lunavt6/Planda/reports and protocols/develop3 - CMF - report.pdf

# CMF report

Onderzoeksvragen
- Welke kleur voor het omhulsel spreekt kinderen van 2–6 jaar het meest aan?
- Welke kleur voor het omhulsel spreekt de ouders het meest aan?
- Welke textuur van het omhulsel is het meest comfortabel voor kinderen van 2–6 jaar?
- Welke kleur voor de oren spreekt kinderen van 2 – 6 jaar het meest aan?
- Welke kleur voor de oren spreekt de ouders het meest aan?

Protocol
Develop3 – CMF – protocol (https://drive.google.com/file/d/153IuJABdIxPPT9onyeNhh-75t1cRlU_d/view?usp=sharing)

Opstelling
Volgende prototypes werden gebruikt naast het tonen van de PowerPoints (zie bijlagen). Kleurgebruik van het omhulsel

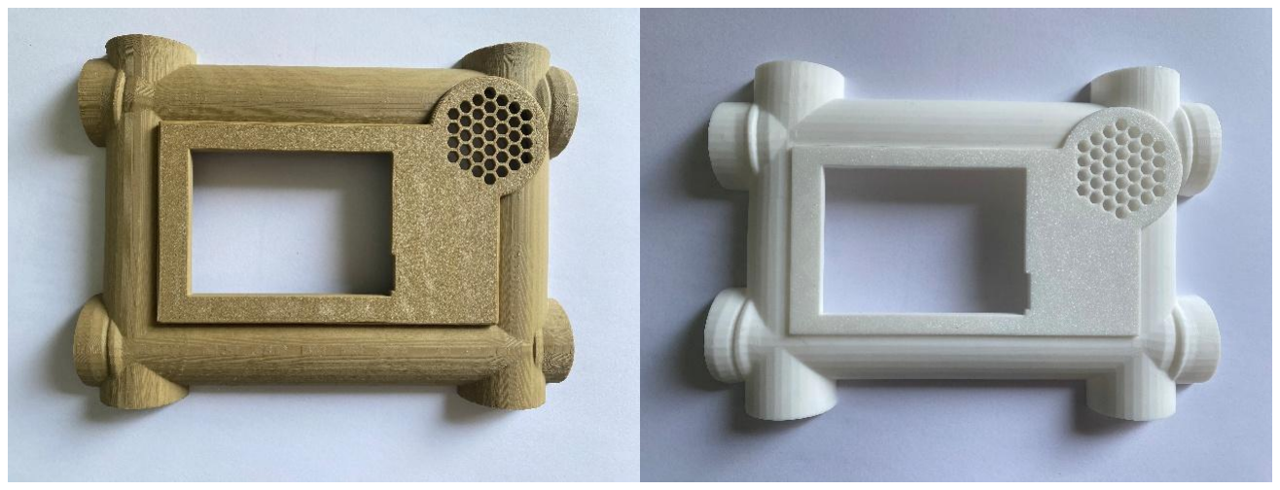
[picture p54: figure]

Figuur 1: Hout | Figuur 2: Wit

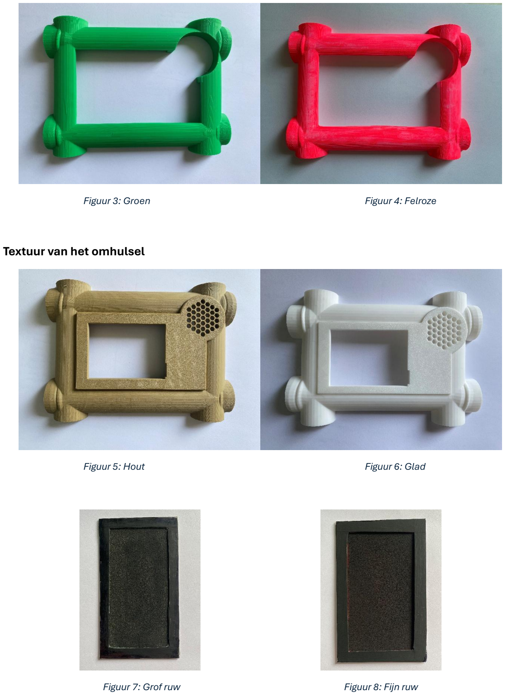
[picture p55: page 2]

Figuur 3: Groen | Figuur 4: Felroze

Textuur van het omhulsel

Figuur 5: Hout | Figuur 6: Glad
Figuur 7: Grof ruw | Figuur 8: Fijn ruw

Observatie
Kleur omhulsel
| Licht hout | Donker hout | Wit | Zwart | Groen | Oranje | Felroze
Kind 1 | | | | | | | X
Kind 2 | | | | | | | X
Kind 3 | | | | | | | X
Ouder 1 | X
Ouder 2 | X | | | | X

Textuur omhulsel
| Hout | Glad | Grof ruw | Fijn ruw
Kind 1 | | | | X
Kind 2 | | X
Kind 3 | | X
Ouder 1 | X
Ouder 2 | X | X

Kleur oren
| Doorzichtig | Transparant | Doorzichtig met rand | Roze | Blauw
Kind 1 | | | X
Kind 2 | | | X
Kind 3 | | | X
Ouder 1 | | | X
Ouder 2 | | | X

Analyse
Kleur omhulsel
Wat betreft het kleurgebruik voor het omhulsel gaven de kinderen duidelijk aan dat ze een voorkeur hebben voor felle, opvallende kleuren. Binnen de voorgestelde opties kwam vooral felroze als favoriete kleur naar voren. Dit staat in contrast met de mening van de ouders. Ouders verkiezen eerder kleuren die aansluiten bij het palet van hun interieur en daardoor minder storend aanwezig zijn in de leefomgeving. Hun voorkeur gaat voornamelijk uit naar neutrale, natuurlijke kleuren en zachte pastelkleuren.
Toch bleek uit de gesprekken dat ouders bereid zijn hierin compromissen te sluiten. Aangezien het product in de eerste plaat bedoeld is voor de kinderen, vinden zij het belangrijk dat het effectief gebruikt wordt en aantrekkelijk is voor hun kind. Wanneer felle kleuren ervoor zorgen dat de panda vaker gebruikt wordt of de interesse van het kind vergroot, staan ouders er dus voor open om af te wijken van hun eigen persoonlijke smaak.

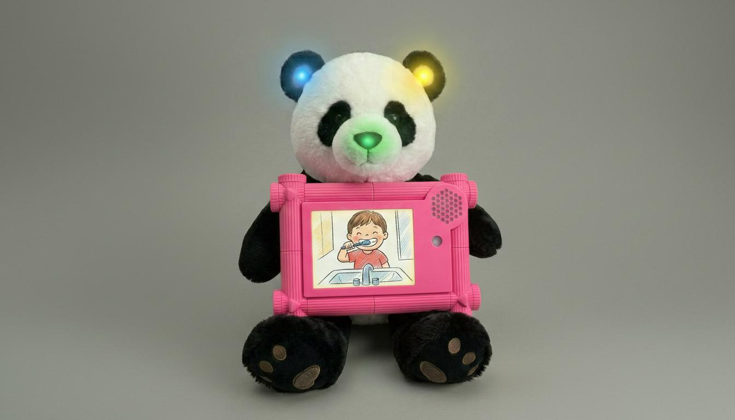
[picture p56: figure]

Figuur 9: Resultaat kleur omhulsel
Hoewel felroze het vaakst gekozen werd als kleur voor het omhulsel, dient opgemerkt te worden dat enkel meisjes deelnamen aan de bevraging. De resultaten kunnen daardoor beïnvloed zijn door persoonlijke of stereotype kleurvoorkeuren en zijn mogelijk niet representatief voor alle kinderen.

Textuur omhulsel
Bij de keuze van de textuur waren de meningen meer verspreid. De antwoorden liepen uiteen tussen de verschillende opties: hout, glad en fijn ruw. Vooral de ouders gaven aan dat ze de houttextuur aantrekkelijk vonden, omdat deze een warme, natuurlijke uitstraling heeft. Het materiaal oogde volgens hen rustgevend en stijlvol.
Toch werd hierbij ook rekening gehouden met het feit dat het uiteindelijke product geen houtkleur zal hebben. Hierdoor zou de houttextuur minder geloofwaardig of passend kunnen overkomen in het definitieve ontwerp. Daarom werd opnieuw gekeken naar de voorkeuren van de kinderen, aangezien zij toch wel de belangrijkste gebruikers van het product zijn.
Uit hun antwoorden bleek dat een gladdere textuur het meest aanspreekt. Een glad oppervlak werd door hen als aangenamer en zachter ervaren, wat beter aansluit bij het speelse en knuffelbare karakter van de panda. Bovendien zorgt een gladde afwerking voor een eenvoudiger en rustiger beeld, waardoor het ontwerp niet te druk wordt.

Kleur oren
Bij de keuze van de oren was er meteen een duidelijke favoriet. Zowel de kinderen als de ouders kozen unaniem voor de optie met een zwart randje. Deze versie werd als de mooiste en meest afgewerkte ervaren. Vooral het zwarte randje rond de oren maakte volgens hen een groot verschil. Daardoor zijn de oren beter zichtbaar en krijgt de panda meer karakter.
Ook zorgde deze optie ervoor dat de panda een herkenbare uitstraling kreeg, want de oren sluiten zo beter aan bij de rest van het ontwerp. Hierdoor oogt het geheel rustiger en samenhangender. Hierdoor kwam de panda aantrekkelijker over dan bij de andere opties.

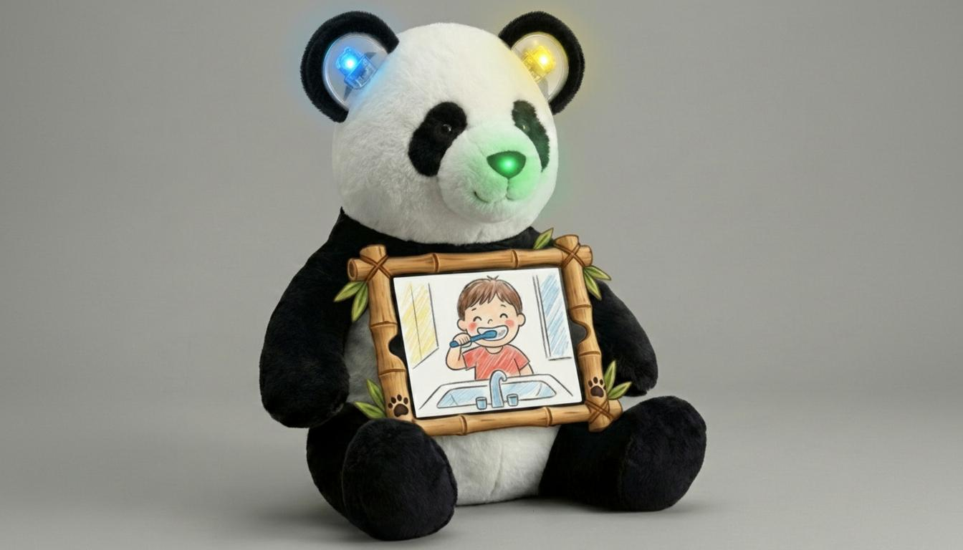
[picture p57: figure]

Figuur 10: Resultaat kleur oren

Conclusie
Uit de analyse blijkt dat kinderen vooral een voorkeur hebben voor felle kleuren en een speels ontwerp, terwijl ouders eerder kiezen voor rustige en natuurlijke tinten. Toch zijn ouders bereid om dit aan te passen als het product daardoor aantrekkelijker wordt voor het kind. De kinderen blijven dus de belangrijkste doelgroep. Daarnaast komt uit de analyse van de textuur naar voren dat een gladde afwerking het meest geschikt is, omdat deze door kinderen als zacht en prettig wordt ervaren en het speelse karakter van de panda versterkt. Ook bij de oren is er een duidelijke overeenstemming: zowel kinderen als ouders verkiezen de variant met een zwart randje, omdat dit zorgt voor meer herkenbaarheid, karakter en een mooi afgewerkt geheel.
De beste keuzes voor het ontwerp zijn daarom een felroze omhulsel, een gladde textuur en oren met een zwart randje. Dit zorgt voor een speels, herkenbaar en aantrekkelijk geheel dat tegelijk voldoende samenhang en rust behoudt.

Tijdens deze fase zijn de volgende design requirements ontstaan.
- Het omhulsel is felroze of een andere felle kleur gericht op de voorkeur van het kind.
- Het oppervlak is glad.
- De oren hebben een zwart randje.

Bijlagen
Develop3 – CMF – kleur omhulsel (https://drive.google.com/file/d/1jtBIYcoHiLNUWgVYdP9SYzcHUyG76-D9/view?usp=sharing) Develop3 – CMF – kleur oren (https://drive.google.com/file/d/1XNqXtDPErmhQJFLdnw9bNmKRSQDc-u7y/view?usp=sharing)
