lunavt6/Planda/reports and protocols/develop1 - literatuuronderzoek - data.pdf

# Literatuuronderzoek data

1. https://www.oudersvannu.nl/kind/de-ontwikkelingsfases-van-je-kind~a67eb44d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 (https://www.oudersvannu.nl/kind/de-ontwikkelingsfases-van-je-kind~a67eb44d)
- 2 – 3 jaar (peuter)
- peuterpuberteit, driftbuien
- overdag zindelijk worden
- begint zich te interesseren in poepen en plassen en kan ook aangeven wanneer hij moet
- middagslaapje wordt overgeslaan
- leert traplopen, rennen en springen
- kan in de speeltuin op steeds meer toestellen, buitenspelen
- fijne motoriek
- leert tekenen (begin: krassen) -> spieren van vingers en handen sterker,
- oefenen van zelf aan- en uitkleden
- samen spelen nog moeilijk
- peuter begrijpt al bijna alles wat je zegt en kan zelf korte zinnetjes terugzeggen
- 3 – 4 jaar (peuter)
- waarom? (nieuwsgierigheid)
- krijgt grote fantasie en gaat magisch denken
- goed rollenspellen doen
- kunnen ook angsten ontstaan (monster in de slaapkamer)
- driftbuien nog altijd, maar kunnen toch al wat beter zich beheersen dan vorige fase
- beginnen begrijpen van gevoelens van zichzelf en anderen
- besef krijgen van wat goed en fout is
- schuldig voelen
- geen middagdutje
- naar kleuterschool gaan -> belangrijk dat bepaalde zaken zelfstandig kunnen
- oefenen van jas en schoenen aandoen, billen afvegen
- 4 – 6 jaar (kleuter)
- Gaat naar school
- Nieuwe wijsheden en vaardigheden
- Vrienden maken
- Naar school gaan vraagt veel energie
- Vermoeidheid
- Driftbuien
- Terugval in zindelijkheid -> tijdelijk
- Terugval in duimen -> tijdelijk
- Meer interesse in eigen lichaam en dat van anderen
- Doktertje spelen
- Vader-en-moedertje spelen
- Verliefd zijn
- Melktanden beginnen uit te vallen
- Motorisch

- Hoger klimmen
- Harder fietsen
- Van grote hoogte naar beneden springen
2. https://www.kindengezin.be/nl/thema/ontwikkeling-en-gedrag
- Grove motoriek
- Hoofd optillen: rond 3 maanden
- Rollen: 4 à 5 maanden
- Zitten
- Met steun: rond 6 maanden
- Alleen: rond 9 maanden
- Kruipen: vanaf 6 à 9 maanden
- Staan: vanaf 6 à 9 maanden
- Lopen: rond 14 à 15 maanden eerste stapjes
- Fijne motoriek
- Grijpreflex
- Pasgeboren baby: handjes altijd gebald tot vuistjes
- 2 maanden: handjes af en toe open en dicht
- 3 maanden: handjes meestal open
- Grijpen:
- Vanaf 3, 5 à 6 maand: gericht grijpen en later ook vast te houden
- Tussen 6 en 9 maanden: voorwerp van de ene naar de andere hand overgeven en 2 voorwerpen tegelijk vasthouden
- Tussen 9 en 12 maanden: klein voorwerp oppakken tussen duim en wijsvinger en/of middenvinger = pincetgreep / tweevingergreep
- Onderzoeken met de handen: tussen 6 en 9 maanden
- met de vlakke hand tegen dingen slaan
- voorwerpen tegen elkaar slaan
- voorwerpen opzettelijk laten vallen
- een handje in een beker stoppen
- vanaf 12 maanden: complexere bewegingen
- Eten met een vork: rond 18 maanden -> wel nog lastig
- Tekenen
- Rond 12 maanden: krassen
- Rond 2 jaar: bewegingen meer beheerst, krassen worden krabbels
- Rond 3 jaar: vormen zichtbaar: losse lijn, kruis, zigzaglijn, vierkant, …
- Na 3 jaar:
- Herkennen wat het getekend heeft, vb rondje -> gezicht of de zon getekend
- Uitbeeldend tekenen
- Meestal mensen en gezichten getekend
- Later armen en benen rechtstreeks aan hoofd getekend = kopvoeters
- Nog later: lijf erbij getekend
- Volgende fase
- Op voorhand plannen wat er op het papier moet komen

- Tekenen van tafereel
- Rond 8 à 9 jaar: tekenen van beelden uit de realiteit, wat ze zien
- Taalontwikkeling
- 15 maanden tot 3 jaar: peuter
- Kent en begrijpt al heel wat woorden
- Vanaf 18 maanden:
- zinnen maken van 2 woorden
- leren van nieuwe woorden
- stelt vragen aan iedereen rondom hem/haar
- tussen 2 en 3 jaar
- zinnen van 3 tot 5 woorden
- meer en meer verschillende woorden gebruiken
- 3 tot 6 jaar: kleuter
- 3 jaar: werkwoorden en meervouden leren gebruiken
- Begrijpen meer en meer wat kleuter zegt
3. https://www.nji.nl/kennis/ontwikkeling/peuter-de-algemene-ontwikkeling
4. https://www.nji.nl/kennis/ontwikkeling/kleuter-de-algemene-ontwikkeling -> zelfde dingen als eerste
5. https://doomijn.nl/blog/de-ontwikkelingsfasen-van-een-kind/
- Motorische ontwikkeling van een peuter
- Meer zelfstandig doen
- Ontwikkelen grove motorische vaardigheden: lopen, rennen, springen, hinkelen, traplopen en fietsen met zijwieltjes
- Ontdekken van activiteiten zoals bouwen, kleuren, kleien, voetballen en verven
- Experimenteren met materialen -> stimuleren van grove en fijne motoriek
- Ontwikkelen fijne motoriek: potlood vasthouden met pengreep ipv vuistgreep
- Cognitieve ontwikkeling van een peuter
- Groei in taalbegrip: peuter begrijpt steeds beter wat er tegen hem gezegd wordt
- Eenvoudige opdrachten uitvoeren
- Vragen beantwoorden
- Ontstaan kleine gesprekjes -> weten wat er in het kind omgaat
- Spraak- en taalontwikkeling van een peuter
- Actief praten en brabbelen
- Eerste echte woorden ontstaan
- Leren ongeveer 3 nieuwe woorden per dag
- Van losse woorden naar twee-woordzinnen
- Ontstaan van korte verhaaltjes en steeds langere, complexere zinnen
- Sociaal-emotionele ontwikkeling van een peuter
- Eigen wil en ik-besef
- Nee-fase, peuterpuberteit en driftbuien
- Nieuwsgierig
- Ontdekken dat wereld groter is dan hun vertrouwde omgeving -> angst en onzekerheid

- Motorische ontwikkeling van een kleuter
- Meer lichaamsbeheersing en soepelere bewegingen
- Starten van zwemles en fietsen zonder zijwieltjes
- Veters strikken en tekeningen worden gedetailleerder
- Melktanden vallen uit
- Naar school gaan
- Cognitieve ontwikkeling van een kleuter
- Leren
- Spelend leren
- Later: leren
- Hoeveelheden
- Plaats
- Tijd
- Ruimtelijke verhouding
- Oorzaak – gevolg
- Spraak- taalontwikkeling van een kleuter
- Letters herkennen
- Leren schrijven
- Complexere taal gebruiken
- Sociaal-emotionele ontwikkeling van een kleuter
- Ontwikkeling van geweten en schaamtegevoelens
- Magisch denken
- Zelfbeeld
- Assertiviteit, morele ontwikkeling, rechtvaardigheidsbesef, identificatie met ouders
6. https://www.ncj.nl/wp-content/uploads/media-import/docs/d5771c50-bac7-4fb6-a307-e302b14d664b.pdf (https://www.ncj.nl/wp-content/uploads/media-import/docs/d5771c50-bac7-4fb6-a307-e302b14d664b.pdf)

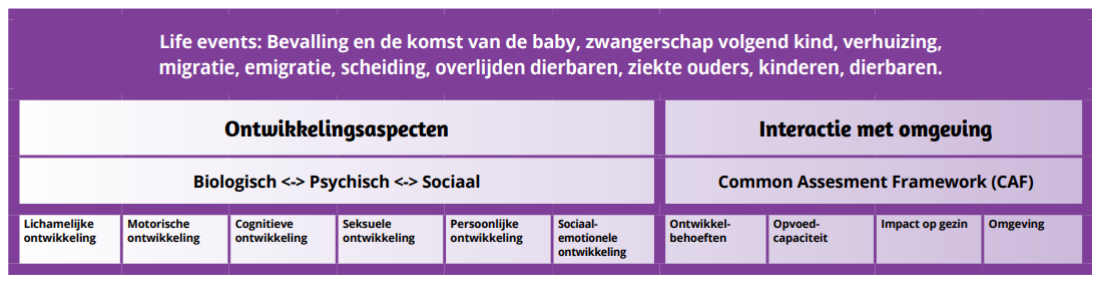
[picture p63: figure]
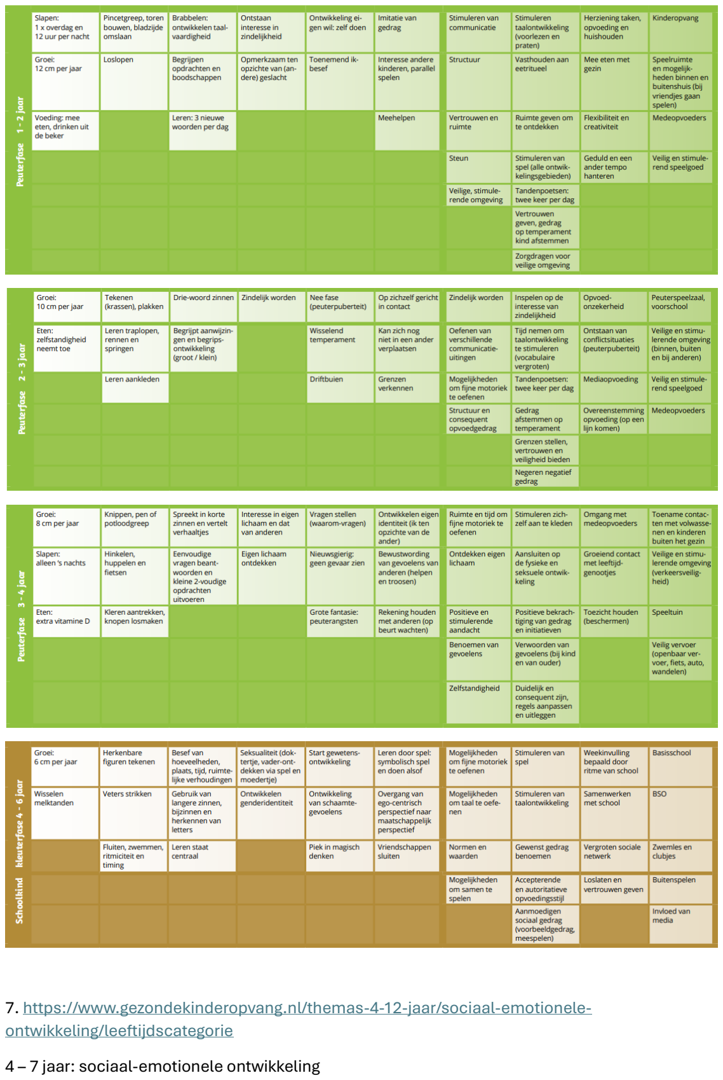
[picture p64: page 5]

7. https://www.gezondekinderopvang.nl/themas-4-12-jaar/sociaal-emotionele-ontwikkeling/leeftijdscategorie (https://www.gezondekinderopvang.nl/themas-4-12-jaar/sociaal-emotionele-ontwikkeling/leeftijdscategorie)
4 – 7 jaar: sociaal-emotionele ontwikkeling

- Meer besef van een eigen ik
- Meer bewustzijn van eigen kwetsbaarheid
- Angstgevoelens
- Leert eigen emoties en die van anderen kennen
- Leren wat wel en niet mag door afspraken / regels
- Empathie en zelfbeheersing zijn belangrijk voor de sociale contacten en vriendschappen
- Waarden en normen beginnen zich net te ontwikkelen
- Goed en slecht zijn nog vage begrippen
- Gedrag van andere kinderen
- Kijken naar materiële gevolgen ipv de reden ervoor
- Vriendschappen nog oppervlakkig en vooral functioneel
- Fantasie en werkelijkheid lopen soms door elkaar
- Emoties nog snel afwisselen
8. https://www.vitakruid.be/blog/belangrijke-mijlpalen-voor-de-ontwikkeling-van-je-kind
| Cognitief | Emotioneel en sociaal | Taal | Sensorisch en motorisch
2 jaar | - Bouwt blokkentorens - Kan eenvoudige instructies opvolgen - Begint eenvoudige tijdconcepten te begrijpen, zoals 'nu', 'later' of 'een paar minuten'. - Begint met het herkennen en sorteren van objecten op vorm en kleur. - Begint met ‘doen alsof’ - Wil vaak twee onverenigbare dingen tegelijk doen, bijvoorbeeld naar buiten in de regen en zijn pantoffels dragen. | - Het ontwikkelen van zelfbewustzijn en het besef dat ze individuen zijn. Hoewel kinderen enthousiast zijn over hun ontwikkeling en vaardigheden, worstelen ze ook vaak met hun ontluikende onafhankelijkheid. Jouw kind kan het ene moment niet getroost willen worden, om het volgende moment zich aan je vast te klampen. - Ze begrijpen en gebruiken het woord 'nee' als een manier om voor zichzelf op te komen. - Geïnteresseerd om met andere kinderen samen te zijn, maar zullen nog niet snel samenspelen. - Geïnteresseerd in het observeren en imiteren van anderen. | - Kan al veel dingen benoemen. - Kan simpele, korte zinnen van twee woorden formuleren, zoals "meer drinken". - Zegt de namen van bekenden. - Spreek met een mix van verzonnen en bestaande woorden. | - Loopt - Springt op en neer - Staat op de tenen - Kan lijnen en ronde vormen tekenen - Gooit ballen - Kan trappen beklimmen met behulp van trapleuning
3 jaar | - Kan een puzzel van 3-4 delen maken - Kan speelgoed gebruiken met bewegende delen zoals knoppen en hendels - Kan deurklinken gebruiken - Kan de bladzijde van een boek omslaan | - Toont empathie voor huilende kinderen - Toont genegenheid - Begrijpt "mijn" en "de jouwe" - Kan van streek raken als routines veranderen - Kan zichzelf aankleden - Snapt wat om de beurt gaan is | - Spreekt met 2-3 zinnen per keer - Kan veel dagelijkse dingen benoemen - Vormt al (redelijk) begrijpelijke zinnen - Begrijpt termen als "in", "aan" en "onder" | - Kan trappen op en af lopen met één voet op elke tree - Loopt en springt - Vangt een bal - Kan van een glijbaan glijden
4 jaar | - Kan misschien tellen - Kan stokfiguren tekenen - Kan voorspellen wat er in een verhaal gaat gebeuren - Kan eenvoudige bordspellen spelen - Kan een paar kleuren, cijfers en letters benoemen | - Speelt met andere kinderen - Praat over wat ze wel en niet leuk vinden - Doen alsof; kan moeite hebben met herkennen wat echt is en wat niet | - Kan praten over wat er gebeurt in de kinderopvang of op school - Spreekt in zinnen - Kan rijmpjes herkennen of zeggen - Kan voor- en achternaam zeggen | - Kan achteruit lopen - Loopt zelfverzekerd de trap op - Wil met andere kinderen sporten - Kan met wat hulp vloeistoffen ergens ingieten.
5 jaar | - Tekent complexere "mensen" - Kan 10 objecten tellen - Kan letters, cijfers en eenvoudige vormen kopiëren - Begrijpt de volgorde van eenvoudige processen - Kan naam en adres zeggen - Kan veel kleuren benoemen | - Is zich bewust van geslacht - Speelt graag met vrienden - Zingt, danst en speelt acteerspelletje - Schakelt tussen luisteren en tegendraads zijn - Kan het verschil zien tussen verzonnen en echt | - Kan verhalen vertellen met een logische volgorde - Reciteert kinderliedjes of zingt liedjes - Kan letters en cijfers noemen - Kan eenvoudige vragen over verhalen beantwoorden | - Kan een schaar gebruiken - Kan ongeveer 10 seconden op één voet staan - Kan schommelen op een schommel - Maakt gebruik van het toilet
6 jaar (– 8 jaar ) | - Kan instructies voltooien met 3 of meer stappen - Kan achteruit tellen - Kent links en rechts - Kan klokkijken | - Werkt samen en speelt met anderen - Kan met zowel jongens als meisjes spelen - Bootst het gedrag van volwassenen na - Voelt jaloezie - Kan bescheiden zijn over lichamen | - Kan boeken lezen - Begrijpt spraak en spreekt goed | - Kan touwtjespringen of fietsen - Kan tekenen of schilderen - Kan tandenpoetsen, haren kammen en basisverzorgingstaken uitvoeren - Kan fysieke vaardigheden oefenen om er beter in te worden
