lunavt6/Planda/reports and protocols/develop1 - literatuuronderzoek - protocol.pdf

# Literatuuronderzoek protocol

Project informatie
Projectnaam: Planda
Dit project richt zich op het ontwikkelen van een slim product om de opvoedstress bij ouders met jonge kinderen te helpen reduceren. Binnen dit thema wordt onderzocht hoe technologie voor kinderen ouders helpt bij de dagelijkse uitdaging van het ouderschap.
Onderzoekers: Luna Van Tittelboom ( luna.vantittelboom@ugent.be ), Doren Vermaut ( doren.vermaut@ugent.be ), Bram Eeckhout ( bram.eeckhout@ugent.be ) Studenten Industrieel Ingenieur Industrieel Ontwerpen

Doelstelling en kadering
In dit project wordt gewerkt aan een slim hulpmiddel dat ouders met jonge kinderen helpt om de opvoedstress te verlichten. Voor veel ouders is het niet eenvoudig om een goede balans te vinden tussen werk, gezin en tijd voor zichzelf. Om beter te begrijpen wat kinderen kunnen op elke leeftijd tussen 2 en 6 jaar wordt een literatuuronderzoek uitgevoerd. Deze analyse heeft als doel inzicht te krijgen in de verschillende ontwikkelingsfasen op verschillende gebieden: motorische ontwikkeling, cognitieve ontwikkeling, taalontwikkeling en sociaal-emotionele ontwikkeling.

Onderzoeksvragen
Hoe ontwikkelen kinderen zich tussen 2 en 6 jaar op motorisch, cognitief, taal- en sociaalemotioneel gebied volgens bestaande wetenschappelijke literatuur?
- Welke motorische vaardigheden ontwikkelen kinderen tussen 2 en 6 jaar per leeftijdsfase?
- Welke variaties in motorische ontwikkeling worden in de literatuur beschreven?
- Hoe verloopt de cognitieve ontwikkeling van kinderen tussen 2 en 6 jaar volgens ontwikkelingspsychologische theorieën?
- Welke cognitieve vaardigheden zijn kenmerkend per leeftijdsfase?
- Welke fasen worden onderscheiden in de taalontwikkeling van kinderen tussen 2 en 6 jaar?
- Hoe ontwikkelt de sociaal-emotionele ontwikkeling zich tussen 2 en 6 jaar?
- Welke gedragen en emoties zijn passend bij elke leeftijd?

Methode
De gebruikte methode is literatuuronderzoek.

Materialen
Het volledige onderzoek wordt online via sites gedaan.

Beschrijving
1. Verschillende bronnen zoeken die de verschillende ontwikkelingsfasen aangeven.
2. Bronnen vergelijken.
3. Conclusies opstellen.
4. Tijdlijn opstellen.

Report
Develop1 – literatuuronderzoek – report (https://drive.google.com/file/d/1lqU_Gb7P2KewI6b2YRbHUHMy500uVC_5/view?usp=sharing)
