lunavt6/Planda/reports and protocols/develop1 - literatuuronderzoek - report.pdf

# Literatuuronderzoek report

Project informatie
Projectnaam: Planda
Dit project richt zich op het ontwikkelen van een slim product om de opvoedstress bij ouders met jonge kinderen te helpen reduceren. Binnen dit thema wordt onderzocht hoe technologie voor kinderen ouders helpt bij de dagelijkse uitdaging van het ouderschap.
Onderzoekers: Luna Van Tittelboom ( luna.vantittelboom@ugent.be ), Doren Vermaut ( doren.vermaut@ugent.be ), Bram Eeckhout ( bram.eeckhout@ugent.be ) Studenten Industrieel Ingenieur Industrieel Ontwerpen

Doelstelling en kadering
In dit project wordt gewerkt aan een slim hulpmiddel dat ouders met jonge kinderen helpt om de opvoedstress te verlichten. Voor veel ouders is het niet eenvoudig om een goede balans te vinden tussen werk, gezin en tijd voor zichzelf. Om beter te begrijpen wat kinderen kunnen op elke leeftijd tussen 2 en 6 jaar wordt een literatuuronderzoek uitgevoerd. Deze analyse heeft als doel inzicht te krijgen in de verschillende ontwikkelingsfasen op verschillende gebieden: motorische ontwikkeling, cognitieve ontwikkeling, taalontwikkeling en sociaal-emotionele ontwikkeling.

Onderzoeksvragen
Hoe ontwikkelen kinderen zich tussen 2 en 6 jaar op motorisch, cognitief, taal- en sociaal-emotioneel gebied volgens bestaande wetenschappelijke literatuur?
- Welke grove en fijne motorische vaardigheden ontwikkelen kinderen tussen 2 en 6 jaar per leeftijdsfase?
- Welke variaties in motorische ontwikkeling worden in de literatuur beschreven?
- Hoe verloopt de cognitieve ontwikkeling van kinderen tussen 2 en 6 jaar volgens ontwikkelingspsychologische theorieën?
- Welke cognitieve vaardigheden zijn kenmerkend per leeftijdsfase?
- Welke fasen worden onderscheiden in de taalontwikkeling van kinderen tussen 2 en 6 jaar?
- Hoe ontwikkelt de sociaal-emotionele ontwikkeling zich tussen 2 en 6 jaar?
- Welke gedragen en emoties zijn passend bij elke leeftijd?

Protocol
Develop1 – literatuuronderzoek – protocol (https://drive.google.com/file/d/1ZBEzt2UaiXR5UtRfP1CJQvO8A5tVIppP/view?usp=sharing)

Data
Develop1 – literatuuronderzoek – data (https://drive.google.com/file/d/1dzY7ee_4ksOIrwapHJ_z9fS_if3WUj7y/view?usp=sharing)

Analyse
De eerste levensjaren van een kind vormen een belangrijke periode voor de verdere ontwikkeling. In deze fase ontwikkelen kinderen zich op verschillende domeinen, namelijk motorisch, cognitief, taalvaardig en sociaal-emotioneel. In dit literatuuronderzoek wordt de ontwikkeling van het kind tussen 0 en 6 jaar besproken, met een focus op de peuter- en kleuterfase.

### 1. Motorische ontwikkeling

De motorische ontwikkeling kan worden onderverdeeld in grove en fijne motoriek. Beide evolueren sterk in de eerste levensjaren.
Grove motoriek
In het eerste levensjaar ontwikkelt het kind verschillende basisvaardigheden zoals het optillen van het hoofd, rollen, zitten, kruipen en uiteindelijk stappen. Rond 14 à 15 maanden zetten de meeste kinderen hun eerste stapjes. Wanneer het kind 2 – 3 jaar is, bevindt het zich in zijn peuterfase. Tijdens deze fase worden bewegingen doelgerichter en krachtiger. Peuters leren lopen, springen en traplopen. Naarmate het kind ouder wordt, neemt de lichaamsbeheersing toe.
Tijdens de kleuterfase (4 – 6 jaar) worden bewegingen complexer en beter gecoördineerd. Kleuters kunnen hoger klimmen, sneller fietsen en gecontroleerd springen. De motorische vooruitgang zorgt ervoor dat kinderen zelfstandiger worden en meer zelfvertrouwen ontwikkelen. Fijne motoriek
De fijne motoriek begint bij reflexmatige grijpreacties bij de baby. Geleidelijk aan evolueert dit naar doelgericht grijpen en het ontwikkelen van de pincetgreep tussen duim en wijsvinger. Rond 12 maanden beginnen kinderen te krassen op papier.
In de peuterfase worden deze krassen meer gecontroleerd en ontstaan eenvoudige vormen. Rond 3 jaar tekenen kinderen herkenbare figuren, zoals losse lijnen en cirkels. Later verschijnen de typische ‘kopvoeters’. In de kleuterfase worden de tekeningen gedetailleerder en plannen kinderen vooraf wat ze willen tekenen.

### 2. Taalontwikkeling

De taalontwikkeling kent een sterke groei tussen 2 en 4 jaar. Rond 18 maanden beginnen kinderen tweewoordzinnen te vormen. Tussen 2 en 3 jaar worden zinnen langer en complexer. Peuters stellen veel vragen en breiden hun woordenschat snel uit.
In de kleuterfase leren kinderen werkwoorden correct vervoegen en meervouden gebruiken. Ze vertellen eenvoudige verhalen en begrijpen steeds complexere instructies. Tegen 5 à 6 jaar kunnen kinderen logische verhalen vertellen met een duidelijke volgorde.

### 3. Cognitieve ontwikkeling

Op cognitief vlak ontwikkelen peuters het vermogen om eenvoudige instructies te begrijpen en oorzaak-gevolgrelaties te ontdekken. Ze beginnen objecten te sorteren op kleur en vorm en ontwikkelen tijdsbegrippen zoals ‘nu’ en ‘later’. Fantasie speelt een grote rol en peuters doen vaak aan magisch denken waarbij ze in hun eigen magische wereld terechtkomen met prinsen, prinsessen en monsters.
In de kleuterfase wordt het denken logischer. Kinderen leren tellen, eenvoudige spelregels begrijpen en onderscheid maken tussen fantasie en werkelijkheid. Ze kunnen voorspellen wat er in een verhaal zal gebeuren en tonen inzicht in ruimtelijk begrippen.

### 4. Sociaal – emotionele ontwikkeling

De peuterfase wordt vaak gekenmerkt door de ‘peuterpuberteit’. Kinderen ontwikkelen een sterk ik-besef en willen zelfstandig handelen. Dit kan leiden tot driftbuien en conflicten. Tegelijkertijd leren ze basisemoties herkennen en tonen ze beginnende empathie.
In de kleuterfase groeit het besef van regels, normen en waarden. Kinderen ontwikkelen een geweten en kunnen zich schuldig voelen. Vriendschappen ontstaan, al zijn deze in het begin nog oppervlakkig en functioneel. Emoties kunnen nog snel wisselen, maar zelfbeheersing neemt toe.

Conclusie
Uit literatuur blijkt dus dat kinderen tussen 0 en 6 jaar een snelle en belangrijke ontwikkeling doormaken. Op motorisch vlak leren ze eerst kruipen en stappen. Later leren ze dan rennen, springen en fietsen. Hun fijne motoriek ontwikkelt van krassen naar gerichte tekeningen. Op taalgebied gaan ze van losse woorden naar volledige zinnen en leren ze steeds meer hun gevoelens en gedachten uit te drukken. Cognitief leren ze oorzaak en gevolg begrijpen en maken ze stap-voor-stap de overgang van fantasie naar meer logisch denken. Ook sociaal-emotioneel groeien ze sterk. Ze ontwikkelen een eigen wil, leren omgaan met emoties en bouwen vriendschappen op.
Uit dit onderzoek wordt duidelijk waarom intuïtief gekozen werd voor de doelgroep van 2 tot 6 jaar. Dit is een fase waarin kinderen enorme ontwikkelingssprongen maken. Ze zijn nieuwsgierig naar de wereld om zich heen, leren steeds zelfstandiger te worden en ontdekken hoe ze met anderen kunnen omgaan. Tegelijk bereiden ze zich voor op de schoolperiode en zetten ze hun eerste stappen in de kleuterschool. In deze jaren wordt de basis gelegd voor latere vaardigheden. Daarom is het begrijpen om deze leeftijdsgroep goed te begrijpen.

Tijdslijn

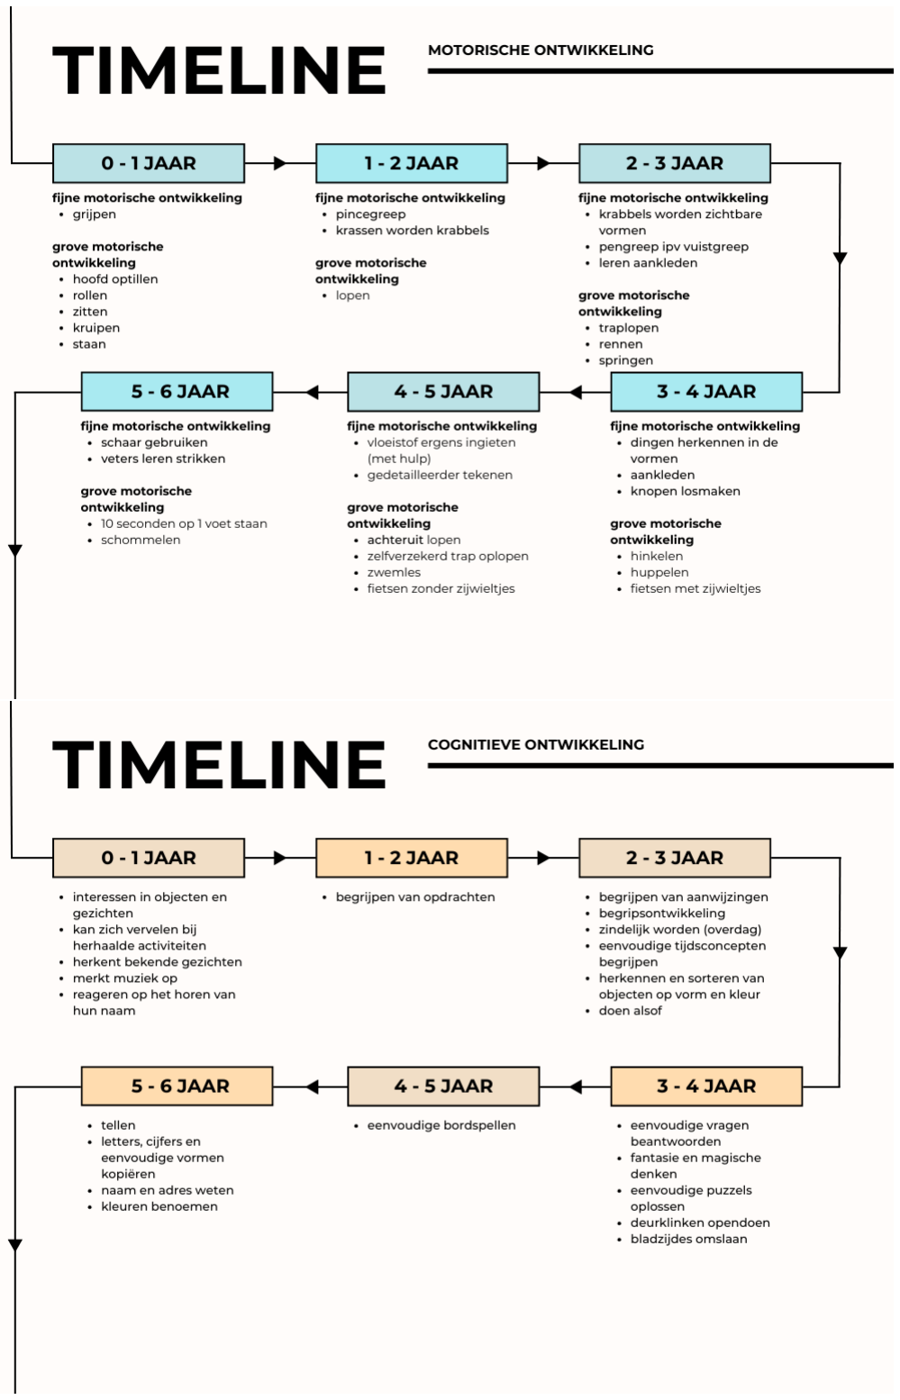
[picture p65: figure]

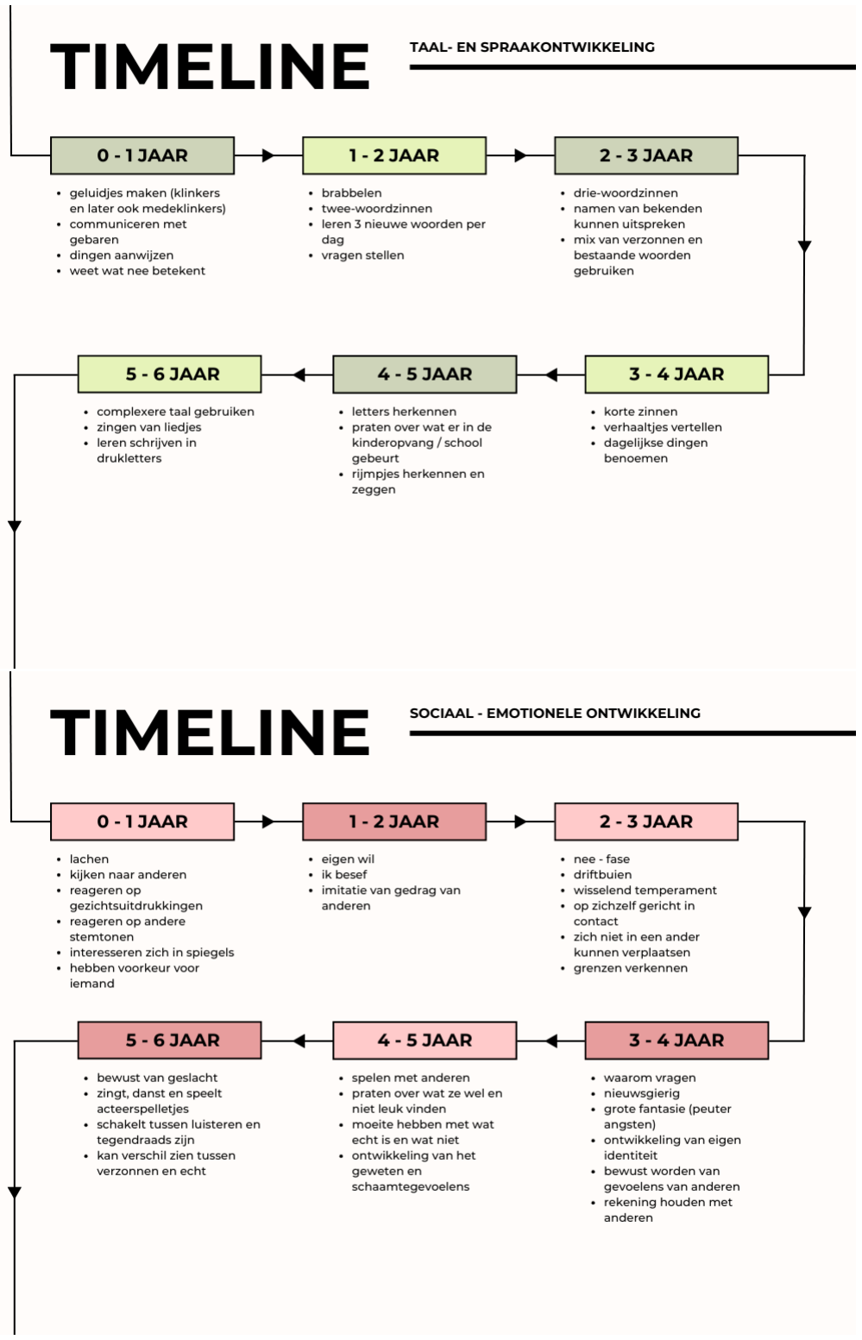
[picture p66: figure]

Bronnen
https://expertisecentrumkinderopvang.nl/images/documenten-openbaar/exb-2018-32453.pdfhttps://www.researchgate.net/publication/341789680_Early_Childhood_Development_0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 (https://www.researchgate.net/publication/341789680_Early_Childhood_Development_0_-_6_Years_Old_from_Healthy_to_Pathologic_A_Review_of_the_Literature) https://www.jstage.jst.go.jp/article/ijshs/2/0/2_0_50/_pdf/-char/jahttps://www.oudersvannu.nl/kind/de-ontwikkelingsfases-van-jekind~a67eb44d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 (https://www.oudersvannu.nl/kind/de-ontwikkelingsfases-van-je-kind~a67eb44d) https://www.kindengezin.be/nl/thema/ontwikkeling-en-gedraghttps://www.nji.nl/kennis/ontwikkeling/peuter-de-algemene-ontwikkelinghttps://www.nji.nl/kennis/ontwikkelin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 (https://www.ncj.nl/wp-content/uploads/media-import/docs/d5771c50-bac7-4fb6-a307-e302b14d664b.pdf)
https://www.gezondekinderopvang.nl/themas-4-12-jaar/sociaal-emotioneleontwikkeling/leeftijdscategorie (https://www.gezondekinderopvang.nl/themas-4-12-jaar/sociaal-emotionele-ontwikkeling/leeftijdscategorie) https://www.vitakruid.be/blog/belangrijke-mijlpalen-voor-de-ontwikkeling-van-je-kind
