lunavt6/Planda/AI_Sfeerfoto.png

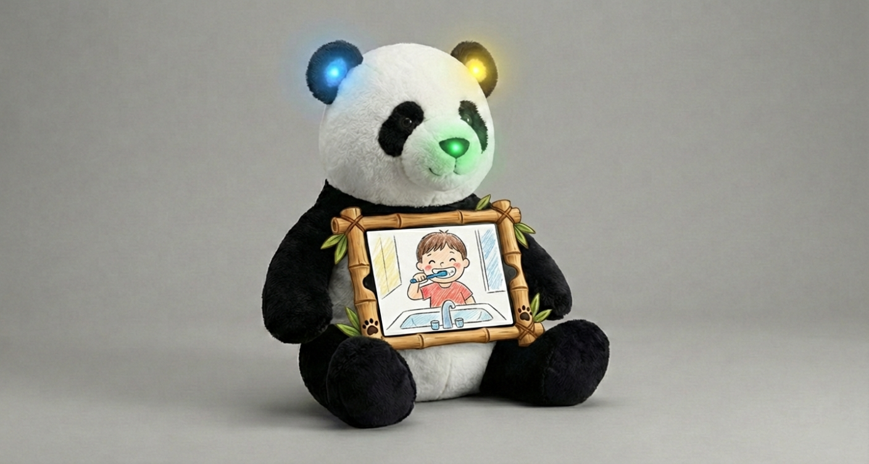
AI_Sfeerfoto.png
