lunavt6/Planda/img/Heroshot_Planda_2.png

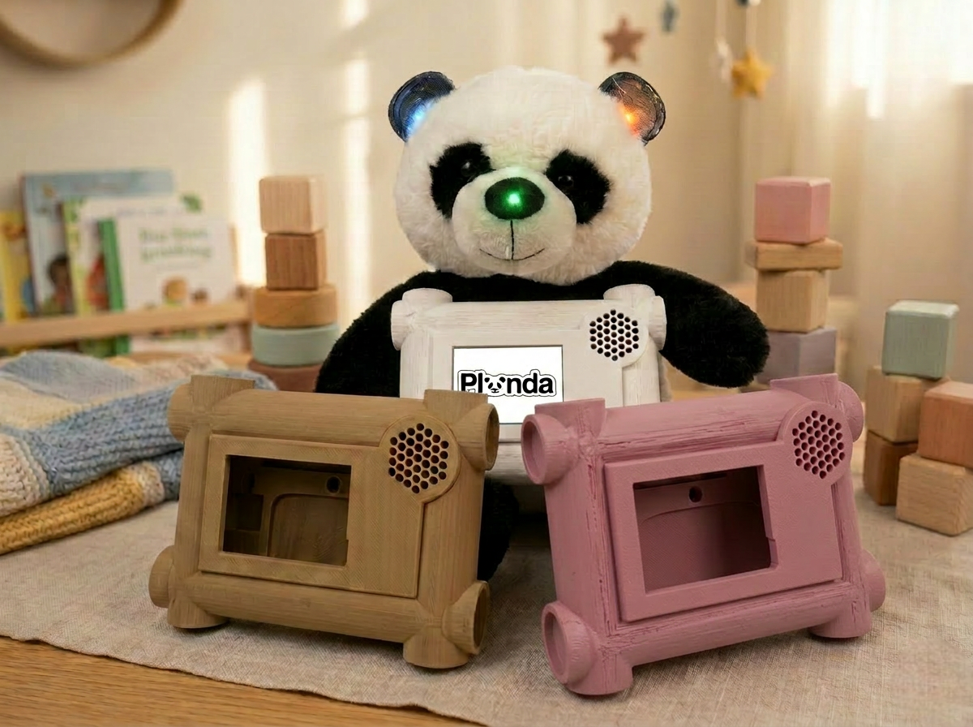
img/Heroshot_Planda_2.png
