lunavt6/Planda/img/omhulsel.png

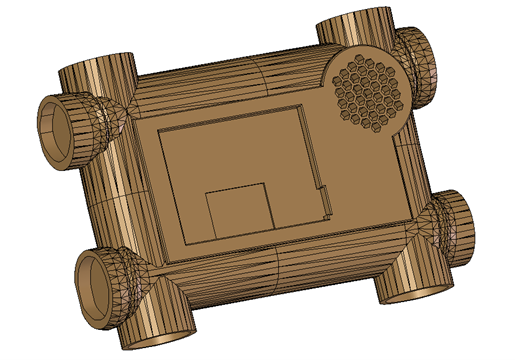
img/omhulsel.png
