lunavt6/Planda/img/render_Planda.png

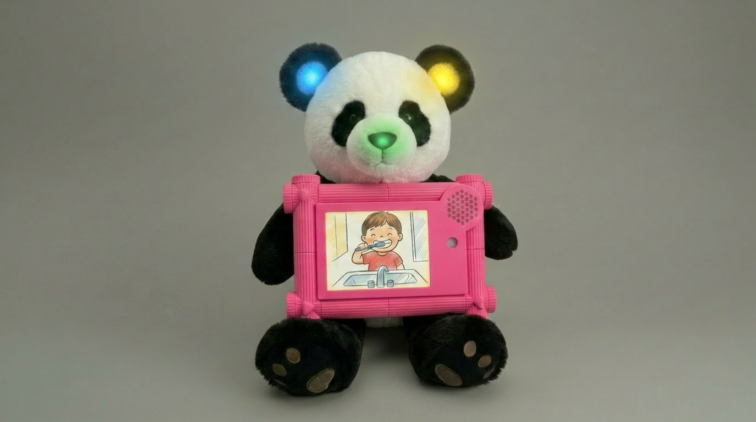
img/render_Planda.png
