lunavt6/Planda/reports and protocols/develop1 - testinterview - protocol.pdf

# Testinterview protocol

Project informatie
Projectnaam: Planda
Dit project richt zich op het ontwikkelen van een slim product om de opvoedstress bij ouders met jonge kinderen te helpen reduceren. Binnen dit thema wordt onderzocht hoe technologie voor kinderen ouders helpt bij de dagelijkse uitdaging van het ouderschap.
Onderzoekers: Luna Van Tittelboom ( luna.vantittelboom@ugent.be ), Doren Vermaut ( doren.vermaut@ugent.be ), Bram Eeckhout ( bram.eeckhout@ugent.be ) Studenten Industrieel Ingenieur Industrieel Ontwerpen

Doelstelling en kadering
In dit project wordt gewerkt aan een slim hulpmiddel dat ouders met jonge kinderen helpt om de stress die optreedt tijdens de ochtendroutine te verlichten. Hierbij gaat het om een pandaknuffel met een schermpje op de buik waarop de taken visueel worden weergegeven. Daarnaast bevinden zich knoppen in de oren van de knuffel. Om beter te begrijpen hoe snel kinderen nieuwe vaardigheden aanleren, worden er testen uitgevoerd waarbij zij een taak met verschillende stappen uitvoeren. Op basis van deze observaties wordt nagegaan wanneer het stappenplan vereenvoudigd kan worden, omdat het kind de vaardigheid al beheerst. Daarnaast wordt onderzocht wat de verwachtingen en wensen van ouders zijn voor de bijhorende app. Hierbij wordt ook bekeken welke elementen nog ontbreken in het huidige prototype, zodat het hulpmiddel verder kan worden afgestemd op de noden van de ouders.

Onderzoeksvragen
Hoe ervaren kinderen van 2–6 jaar de interactie met de interactieve beer tijdens het uitvoeren van de taken?
- Hoe kan het stappenplan van de interactieve beer worden aangepast aan het niveau van het kind?
- Welke impact heeft de fysieke gebruikscontext op het ontwerp van de interactieve interface?
- Hoe moeten visuele instructies ontworpen worden zodat kinderen van 2–6 jaar ze zelfstandig en correct begrijpen?
- Welke rol speelt audiofeedback in het begrijpen van de taak, de motivatie en de zelfstandigheid van jonge kinderen tijdens de taken?
Hoe kan de app optimaal aansluiten bij de behoeften en verwachtingen van ouders van jonge kinderen?
- Welke verwachtingen en wensen hebben ouders over de app?
- Welke elementen of functies ontbreken volgens ouders in het huidige prototype van de app?

Beschrijving van de testopstelling
De gebruikerstesten werden uitgevoerd aan de hand van een Wizard of Oz-opstelling. Hiervoor werd een knuffelbeer gebruikt waarin een smartphone bevestigd was ter hoogte van de buik. Op deze smartphone werd het ontworpen interface (Figma-prototype) weergegeven. De interactie met de beer gebeurde via twee oortjes, die in deze testfase fungeerden als gesimuleerde fysieke knoppen.
Het prototype werd op afstand bediend met behulp van een Bluetooth-muis. Wanneer het kind één van de oortjes indrukte, observeerde ik dit vanop afstand en activeerde ik handmatig de overeenkomstige actie binnen het prototype. Op deze manier werd de indruk gewekt dat de beer zelf reageerde op de input van het kind, terwijl de interactielogica in werkelijkheid door de onderzoeker werd aangestuurd.
Tijdens de test doorliepen de kinderen verschillende taakjes (zoals handen wassen) via de stappen die op het scherm werden weergegeven. De focus lag hierbij op het observeren van begrip, motivatie, interactiegedrag en eventuele moeilijkheden tijdens het uitvoeren van de handelingen.
In deze testfase was er nog geen audiofunctionaliteit geïntegreerd in het prototype. Aangezien de kinderen binnen de doelgroep nog niet vlot kunnen lezen, werden de instructies telkens hardop voorgelezen door de onderzoeker. Hierbij werd de rol van de toekomstige ingebouwde speaker in de beer gesimuleerd. Op deze manier kon toch getest worden hoe auditieve begeleiding de duidelijkheid en betrokkenheid van het kind beïnvloedt.
Deze aanpak maakte het mogelijk om de functionele werking, interactiestroom en gebruikservaring te evalueren zonder dat de technische implementatie reeds volledig ontwikkeld moest zijn.

Overzicht van de discussiegids en tijdsinschatting
- Deel 1 – Introductie (5’)
- Deel 2 – Taak verloop (10’)
- Deel 3 – App prototype (5’)
- Deel 4 – Wrap-up (5’)

Discussiegids

Introductie (5 min.)
Bedankt voor je deelname aan dit onderzoek.

Ik zal starten met het project en mezelf kort voor te stellen.

Ik ben <eigen naam> en ik studeer aan de universiteit Gent campus Kortrijk met afstudeerrichting industrieel ingenieur industrieel ontwerpen.

Deze afstudeerrichting focust zich op het bedenken en verbeteren van producten. Daarom hebben we het vak Project Gebruiksgericht Ontwerpen, waarin we aan de hand van een specifiek thema een prototype moeten maken.

Het thema van dit jaar is opvoedstress. Er moet een slim product worden ontworpen voor ouders die stress ervaren bij de opvoeding van hun kind(eren) tussen de 2 en 6 jaar. Het doel van dit product is om die stress te verminderen. Samen met mijn teamgenoten werken wij aan een product voor de ochtendroutine en eventueel ook de avondroutine.

Dit gesprek is belangrijk omdat ik wil begrijpen hoe snel kinderen taken leren en feedback te krijgen op ons voorlopig prototype van de app.

Ik start dit gesprek graag met vragen over het taakverloop en dan vervolgens stel ik onze eerste prototype van de app voor, zodat we de bevindingen onmiddellijk in de praktijk kunnen uittesten.

Ik ben erg benieuwd naar uw inzichten en ervaringen. Er zijn geen juiste of foute antwoorden. Ik ben gebaat bij uw oprechte feedback rond de topics die we zullen behandelen.

Ik wil zeker nog onderstrepen dat alles wat straks in het gesprek aan bod komt in absolute confidentialiteit behandeld wordt. We zijn als studenten aan de Ugent namelijk gebonden aan de Europese privacy richtlijnen. Voor de synthese met de inzichten en aanbevelingen worden individuele meningen sowieso ook geanonimiseerd. Je naam zal met andere woorden niet gekoppeld worden aan specifieke uitspraken. Een meer gedetailleerde beschrijving van onze intenties, verwerking van gegevens, en algemeen beleid kan je nalezen in de ‘Informed Concent’. Voor we van start kunnen met het interview, heb ik jouw expliciet akkoord nodig met dit document.

Ten slotte, had ik je ook graag gevraagd of ik straks dit gesprek mag opnemen met een voice recorder, om ons gesprek te kunnen herbeluisteren wanneer de analyse wordt gemaakt. Uiteraard wordt deze opname niet gedeeld met derden, en verwijderd na afloop van het project. Als u hiermee akkoord gaat, stel ik voordat we het interview beginnen.

----------------------------[invullen informed consent & start recording] ----------------------------

Contextuele vragen
Taak verloop (Tijdens de gebruikerstesten) (10 min.)
- Aanpassen van het stappenplan aan het niveau
- Hoe zelfstandig voert het kind deze taak normaal gezien uit zonder begeleiding?
- Waren de stappen te uitgebreid, te beknopt of net goed voor dit kind?
- Op welke momenten ging het tempo te traag of te snel?
- Denkt u dat uw kind nood heeft aan meer detail of net minder uitleg?
- Hoe merkt u in het dagelijks leven dat uw kind klaar is voor minder begeleiding?
- Impact van de fysieke gebruikscontext
- Waar staat de beer tijdens de taak en was dat volgens u een goede plaats?
- Waarom wel? Waarom niet?
- Ontwerp van visuele instructies
- Begrijpt uw kind wat het moest doen door alleen naar het scherm te kijken?
- Waren bepaalde afbeeldingen of pictogrammen onduidelijk?
- Bij welke stappen heeft uw kind extra uitleg nodig?
- Rol van audiofeedback
- Is er een verschil in reactietijd wanneer de taak wordt voorgelezen?
- Hoe reageert uw kind op aanmoedigende woorden?

App prototype (5 min.)
- Wat zijn uw verwachtingen en wensen bij de bijhorende app?
- Wat moet er zeker in zitten?
- Welke elementen of functies ontbreken volgens u in het huidige prototype van de app?

Wrap-up (5 min.)
Wenst u zelf nog zaken toe te voegen?
De belangrijkste zaken die ik heb geleerd uit dit interview zijn, … Heb ik het juist begrepen als …?

Wat zijn de belangrijkste elementen waarvan u denkt dat ik die het meest zou moeten onthouden?
Zou u graag op de hoogte blijven van de resultaten of toekomstige gebruikerstests? Bedankt voor uw tijd en medewerking.

Report
Develop1 – testinterview – report (https://drive.google.com/file/d/1iAICvbYoYDdQVMLRW9RndhLdhfBj4c1h/view?usp=sharing)
