lunavt6/Planda/reports and protocols/discovery - benchmarking - protocol.pdf

# Benchmarking protocol

Project informatie
Projectnaam: Opvoedstress
Dit project richt zich op het ontwikkelen van een slim product om de opvoedstress bij ouders met jonge kinderen te helpen reduceren. Binnen dit thema wordt onderzocht hoe technologie voor kinderen ouders helpt bij de dagelijkse uitdaging van het ouderschap.
Onderzoeker: Luna Van Tittelboom ( luna.vantittelboom@ugent.be ), Student Industrieel Ingenieur Industrieel Ontwerpen

Doelstelling en kadering
In dit project wordt gewerkt aan een slim hulpmiddel dat ouders met jonge kinderen helpt om de opvoedstress te verlichten. Voor veel ouders is het niet eenvoudig om een goede balans te vinden tussen werk, gezin en tijd voor zichzelf. Om beter te begrijpen welke bestaande oplossingen er al zijn en op welke taken nog weinig ondersteuning wordt geboden, wordt er een benchmarking uitgevoerd. Deze analyse heeft als doel te laten zien welke oplossingen er al bestaan en waar nog weinig hulp is, zodat het nieuwe hulpmiddel zich richt op wat ouders echt nodig hebben en goed aansluit bij hun leefwereld.

Onderzoeksvragen
Hoe kan een slim product ervoor zorgen dat ouders met kinderen tussen 2 en 6 jaar minder stress ervaren bij een specifieke taak die hun kind moet uitvoeren?
- Welke oplossingen bestaan er al?
- Voor welke (dagelijkse) taak zijn nog het minst oplossingen beschikbaar?

Methode
De gebruikte methode is benchmarking.

Materialen
De volledige benchmarking wordt online via sites gedaan.

Beschrijving
1. Producten bij verschillende taken opzoeken.
2. Beschrijving van het product.
3. Sterktes en zwaktes van het product.
4. Conclusie.

Report
Benchmarking - report - opvoedstress (https://drive.google.com/file/d/1ek-WHoF4-XrpG6pTKncxjXwMrDPfr108/view?usp=sharing)
